photomattmills/ourglass/ourglass/analog_constants.cpp

#include "Arduino.h"
const int hour_x_point_1[]={67, 66, 65, 64, 63, 62, 60, 59, 59, 58, 56, 56, 55, 55, 54, 54, 54, 53, 53, 54, 53, 54, 55, 55, 56, 56, 57, 58, 59, 60, 61, 62, 63, 64, 65, 66, 68, 69, 69, 70, 72, 72, 73, 73, 74, 74, 74, 75, 75, 74, 75, 74, 73, 73, 72, 72, 71, 70, 69, 68};
const uint8_t hour_x_point_2[]={61, 60, 59, 58, 57, 56, 56, 55, 55, 54, 54, 54, 53, 53, 54, 54, 54, 55, 55, 56, 57, 58, 59, 59, 60, 62, 63, 64, 65, 66, 67, 68, 69, 70, 71, 72, 72, 73, 73, 74, 74, 74, 75, 75, 74, 74, 74, 73, 73, 72, 71, 70, 69, 69, 68, 66, 65, 64, 63, 62};
const uint8_t hour_x_point_3[]={61, 65, 69, 73, 77, 81, 86, 89, 92, 94, 98, 100, 101, 102, 104, 104, 104, 104, 103, 102, 101, 98, 96, 93, 90, 87, 83, 79, 75, 71, 67, 63, 59, 55, 51, 47, 42, 39, 36, 34, 30, 28, 27, 26, 24, 24, 24, 24, 25, 26, 27, 30, 32, 35, 38, 41, 45, 49, 53, 57};
const uint8_t hour_x_point_4[]={67, 71, 75, 79, 83, 87, 90, 93, 96, 98, 100, 102, 103, 104, 104, 104, 104, 102, 101, 100, 97, 94, 92, 89, 86, 81, 77, 73, 69, 65, 61, 57, 53, 49, 45, 41, 38, 35, 32, 30, 28, 26, 25, 24, 24, 24, 24, 26, 27, 28, 31, 34, 36, 39, 42, 47, 51, 55, 59, 63};
const uint8_t hour_y_point_1[]={74, 74, 75, 75, 74, 75, 74, 73, 73, 72, 72, 71, 70, 69, 68, 67, 66, 65, 64, 63, 62, 60, 59, 59, 58, 56, 56, 55, 55, 54, 54, 54, 53, 53, 54, 53, 54, 55, 55, 56, 56, 57, 58, 59, 60, 61, 62, 63, 64, 65, 66, 68, 69, 69, 70, 72, 72, 73, 73, 74};
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

// This also looks dumb, I know. The fastest way to write the hour markers to
// the screen is to store them as a byte array and memcopy it into place.
const uint8_t watchFace[]= {0xff, 0xff, 0xff, 0xc1, 0xff, 0xff, 0xff, 0x3f, 0xf8, 0xff, 0xff, 0xff, 0x0f, 0xfe, 0xff, 0xff, 0xff, 0xff, 0xff, 0xc1, 0xff, 0xff, 0xff, 0x3f, 0xf8, 0xff, 0xff, 0xff, 0x0f, 0xfe, 0xff, 0xff, 0xff, 0xff, 0xff, 0x83, 0xff, 0xff, 0xff, 0x3f, 0xf8, 0xff, 0xff, 0xff, 0x07, 0xff, 0xff, 0xff, 0xff, 0xff, 0xff, 0x83, 0xff, 0xff, 0xff, 0x3f, 0xf8, 0xff, 0xff, 0xff, 0x07, 0xff, 0xff, 0xff, 0xff, 0xff, 0xff, 0x07, 0xff, 0xff, 0xff, 0xff, 0xff, 0xff, 0xff, 0xff, 0x83, 0xff, 0xff, 0xff, 0xff, 0xff, 0xff, 0x07, 0xff, 0xff, 0xff, 0xff, 0xff, 0xff, 0xff, 0xff, 0x83, 0xff, 0xff, 0xff, 0xff, 0xff, 0xff, 0x0f, 0xfe, 0xff, 0xff, 0xff, 0xff, 0xff, 0xff, 0xff, 0xc1, 0xff, 0xff, 0xff, 0xff, 0xff, 0xff, 0x0f, 0xfc, 0xff, 0xff, 0xff, 0xff, 0xff, 0xff, 0xff, 0xe0, 0xff, 0xff, 0xff, 0xff, 0xff, 0xff, 0x1f, 0xfc, 0xff, 0xff, 0xff, 0xff, 0xff, 0xff, 0xff, 0xe0, 0xff, 0xff, 0xff, 0xff, 0xff, 0xff, 0x3f, 0xf8, 0xff, 0xff, 0xff, 0xff, 0xff, 0xff, 0x7f, 0xf0, 0xff, 0xff, 0xff, 0xff, 0xff, 0xff, 0x3f, 0xf8, 0xff, 0xff, 0xff, 0xff, 0xff, 0xff, 0x7f, 0xf0, 0xff, 0xff, 0xff, 0xff, 0xff, 0xff, 0x7f, 0xf8, 0xff, 0xff, 0xff, 0xff, 0xff, 0xff, 0x3f, 0xf8, 0xff, 0xff, 0xff, 0xff, 0xff, 0xff, 0x7f, 0xfc, 0xff, 0xff, 0xff, 0xff, 0xff, 0xff, 0x7f, 0xf8, 0xff, 0xff, 0xff, 0xff, 0xff, 0xff, 0xff, 0xff, 0xff, 0xff, 0xff, 0xff, 0xff, 0xff, 0xff, 0xfd, 0xff, 0xff, 0xff, 0xff, 0xff, 0xff, 0xff, 0xff, 0xff, 0xff, 0xff, 0xff, 0xff, 0xff, 0xff, 0xff, 0xff, 0xff, 0xff, 0xff, 0xff, 0xff, 0xff, 0xff, 0x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
ff, 0xe0, 0xff, 0xff, 0xff, 0xff, 0xff, 0xff, 0x83, 0xff, 0xff, 0xff, 0x3f, 0xf8, 0xff, 0xff, 0xff, 0xc1, 0xff, 0xff, 0xff, 0xff, 0xff, 0xff, 0x83, 0xff, 0xff, 0xff, 0x3f, 0xf8, 0xff, 0xff, 0xff, 0xc1, 0xff, 0xff, 0xff, 0xff, 0xff, 0xff, 0xc1, 0xff, 0xff, 0xff, 0x3f, 0xf8, 0xff, 0xff, 0xff, 0x83, 0xff, 0xff, 0xff};
